IanEdwards99/Ultrasonic_doppler_radar/Prototyping/RxCircuit.png

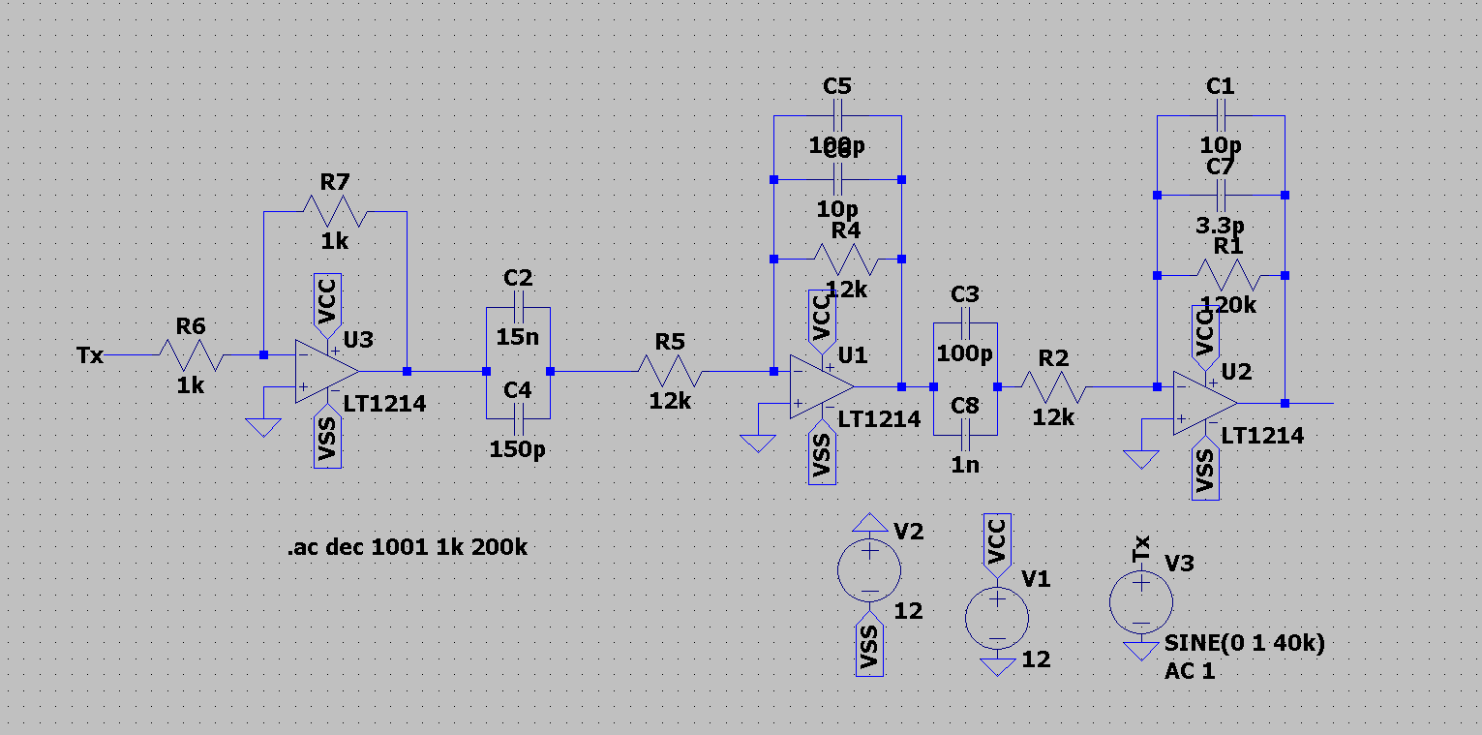
Prototyping/RxCircuit.png
