IanEdwards99/Ultrasonic_doppler_radar/Prototyping/Draft1.asc

R1: res; 12k
R2: res; 12k
U1: 7912
U2: 7812
V1: voltage; 24
Named nets: 0, +12V, -12V
.tran 1s
