IanEdwards99/Ultrasonic_doppler_radar/Prototyping/PowerSupply.asc

R1: res; 12k
R2: res; 12k
U1: LT1214
X1: MT3608
Named nets: 12V, 0, +12V, -12V, V_Ground
24V
