IanEdwards99/Ultrasonic_doppler_radar/Prototyping/RxFinal.asc

C1: cap; 15n
C2: cap; 150p
C3: cap; 100p
C4: cap; 10p
C5: cap; 3.3p
C6: cap; 10p
C7: cap; 100p
C8: cap; 1n
C9: polcap; 100n
C10: cap; 100µ
C11: cap; 1µ
C12: cap; 1µ
D1: schottky; 1N5819
D2: schottky; 1N5819
R1: res; 120k
R2: res; 12k
R3: res; 12k
R4: res; 12k
R5: res; 12k
R6: res; 10k
R7: res; 1k
R8: res; 12k
R9: res; 12k
R11: res; 3.3k
R12: res; 12k
U1: LT1214
U2: LT1214
U3: LT1214
U4: LT1214
V1: voltage; 12
V2: voltage; 12
V3: voltage; SINE(0 0.05 40k); AC 1 0
Named nets: 0, VCC, VSS, 3.3V, Rx
.ac dec 1001 0.5k 200k
10k pot
10k pot
;.tran 0.1m
