IanEdwards99/Ultrasonic_doppler_radar/Prototyping/splitter.asc

R1: res; 12k
R2: res; 12k
U1: LT1214
V1: voltage; 24
Named nets: 0
.tran 1m
