IanEdwards99/Ultrasonic_doppler_radar/Prototyping/TxFinal.asc

C1: cap; 330p
C2: cap; 100p
C3: cap; 47p
C4: cap; 220p
C5: cap; 3.3p
C6: cap; 22p
C7: cap; 330p
C8: cap; 68p
R1: res; 120k
R2: res; 12k
R3: res; 12k
R4: res; 12k
R5: res; 10k
R6: res; 1k
U1: LT1214
U2: LT1214
U3: LT1214
V1: voltage; 12
V2: voltage; 12
V3: voltage; SINE(0 1 40k); AC 1 0
Named nets: 0, VCC, VSS, SC, TX
.ac dec 1001 10k 150k
10k Pot
